MarkusVLA/Suunnattava-suuntamikrofoni/images/Beam_pattern_2kHz.png

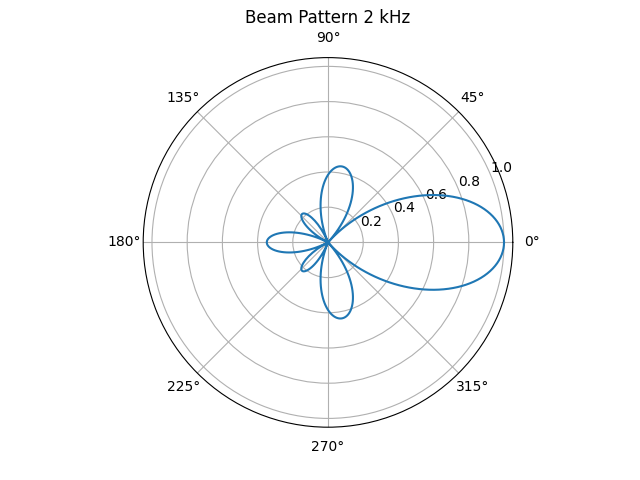
images/Beam_pattern_2kHz.png
