MarkusVLA/Suunnattava-suuntamikrofoni/low-pass-filter/Simulation/3rd order low pass filter.asc

C1: cap; 680p
C2: cap; 47p
C3: cap; 330p
R1: res; 12k
R2: res; 110k
R3: res; 36k
U1: UniversalOpAmp
V1: voltage; SINE(0 1 1k); AC 1 0
V2: voltage; 10
V3: voltage; 10
Named nets: Vin, 0, Vout, Vp, Vn
.ac dec 100 1 100k
